WeirWeather/WeirWeather-AWS/minutes/Group Meetings/Group Meeting 9 - 04-10-19.pdf

04/11/19 | Meeting Minutes | WeirWeather
Group Meeting 9 | 1

# WeirWeather Group Meeting 9 Minutes

Date: 11:00, Mon 04/11/19 | Room: RC473
Minute Taker: Tesfu Gebremedhin

## 1 Attendance

Zack North, Callum Brooksby, Tesfu Gebremedhin, Alexander Ulrichsen, Mario Manca

## 2 Announcements

Only having one meeting every week on Mondays

## 3 Review Previous Meeting Minutes

The previous meeting’s minutes were reviewed and accepted by the group.

## 4 Actions from Last Meeting

# | Action | Assigned To | Progress

1 | Competitor Analysis | All | Done
2 | Background Research Tasks | All | Done

## 5 Agenda

- Update meeting
- Check logbooks
- Decide actions for next week

## 6 Actions

# | Action | Assigned To | Progress

1 | Complete PDS | All | Done
2 | Organise Roof Access | Alexander | Done
3 | Create a database | Alexander | Done
4 | Email Professor Macdonald regarding web server | Alexander | Done
5 | Wind Speed Requirements | Tesfu | Done
6 | Wind Direction Requirements | Tesfu | Done
7 | Daylight Hours Requirements | Tesfu | Done
8 | Web Server Requirements | Callum | Done
9 | Website GUI Requirements | Callum | Done
10 | Microcontroller Requirements | Zack | Done

04/11/19 | Meeting Minutes | WeirWeather
Group Meeting 9 | 2
11 | Solar Panel Requirements | Zack | 08/11/19
12 | Battery & Controller Requirements | Zack | 08/11/19
13 | Rain Gauge Requirements | Mario | 08/11/19
14 | Temperature and Humidity Requirements | Mario | 08/11/19
15 | Barometric Pressure Requirements | Mario | 08/11/19
