WeirWeather/WeirWeather-AWS/software/Website/Images/james.png

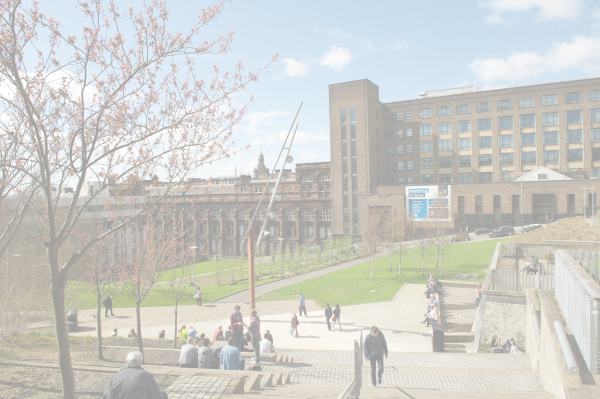
software/Website/Images/james.png
