WeirWeather/WeirWeather-AWS/hardware/Complete CAD Assembly/3D Print/Wind Vane Print.stl

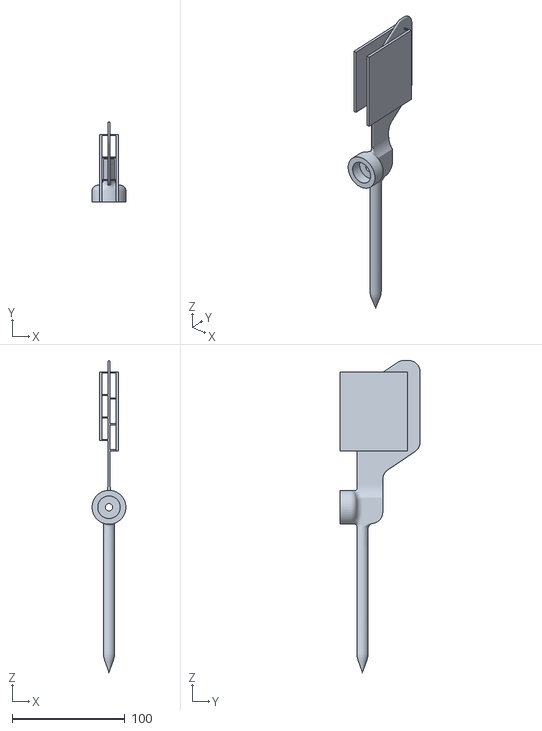
[picture p27: CAD file, 2020-04-21]
hardware/Complete CAD Assembly/3D Print/Wind Vane Print.stl
30.0 x 71.0 x 276.4
