WeirWeather/WeirWeather-AWS/hardware/Complete CAD Assembly/PCB CAD/anemometer_v4.step

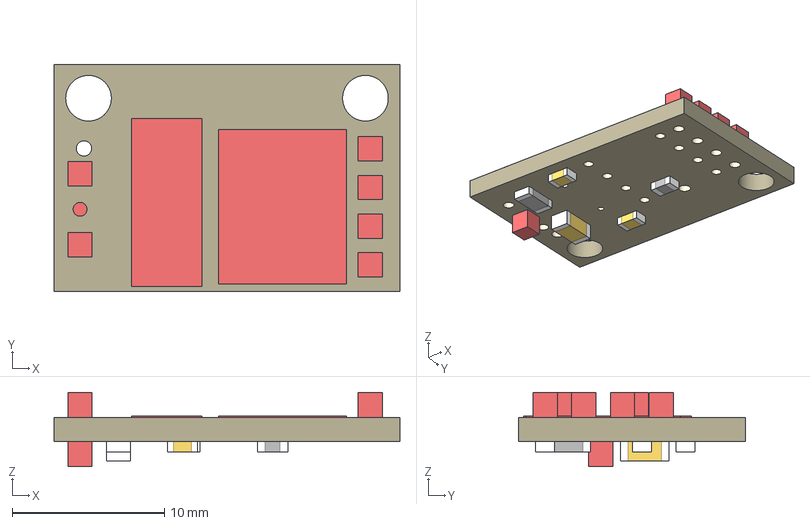
[picture p28: CAD file, 2020-04-21]
hardware/Complete CAD Assembly/PCB CAD/anemometer_v4.step
22.7 x 14.9 x 4.89 mm
Board
1,6/0,9 x 7
4.7k
100n
ATTINY85-P
QCL16.0000F18B23B
18 pF x 2
10k
