WeirWeather/WeirWeather-AWS/hardware/Complete CAD Assembly/Radiation Sheild/HTU21D_mount_V1.stl

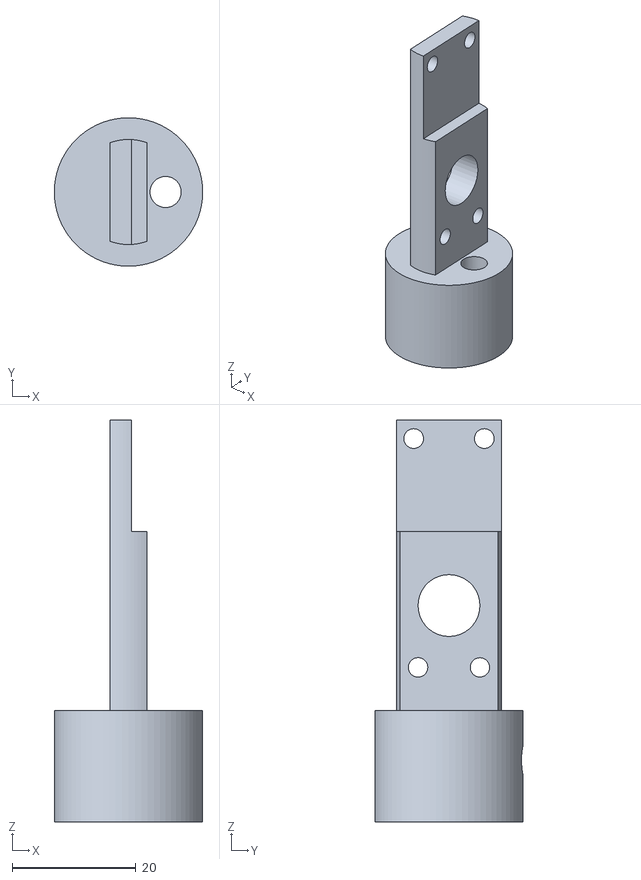
[picture p29: CAD file, 2020-04-21]
hardware/Complete CAD Assembly/Radiation Sheild/HTU21D_mount_V1.stl
24.0 x 24.0 x 65.0
