WeirWeather/WeirWeather-AWS/hardware/Rain Gauge/CAD/STLs/Base.stl

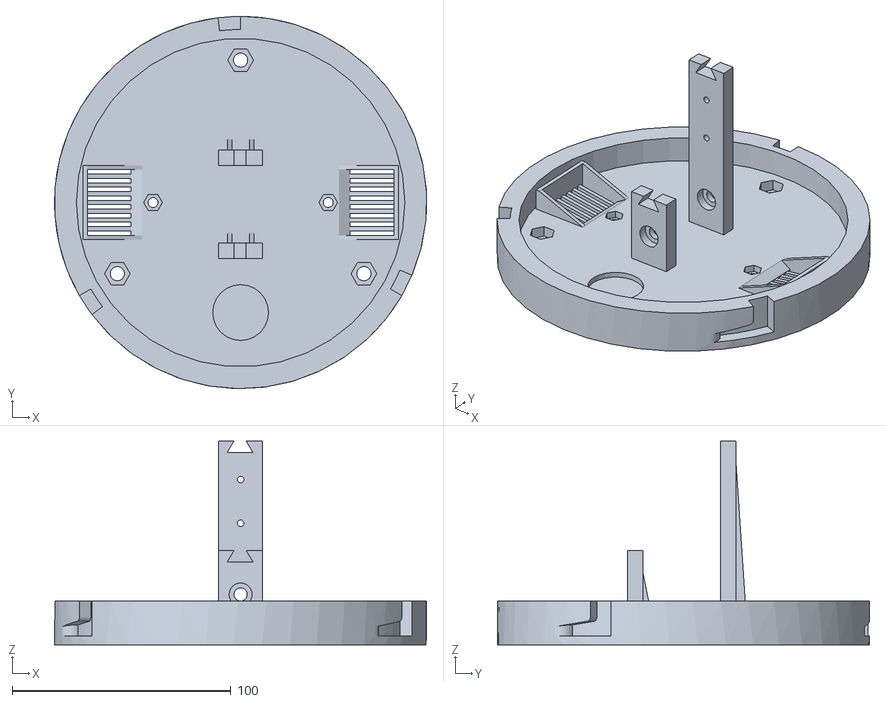
[picture p30: CAD file, 2020-04-16]
hardware/Rain Gauge/CAD/STLs/Base.stl
169.9 x 170.0 x 93.0
