WeirWeather/WeirWeather-AWS/hardware/Complete CAD Assembly/3D Print/Bottom.stl

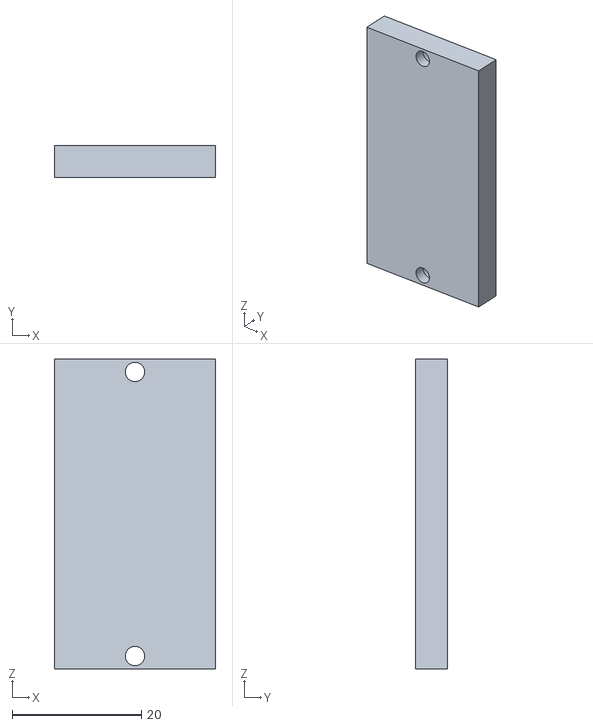
[picture p31: CAD file, 2020-04-21]
hardware/Complete CAD Assembly/3D Print/Bottom.stl
25.0 x 5.00 x 48.0
