WeirWeather/WeirWeather-AWS/hardware/Complete CAD Assembly/PCB CAD/Four_Sensors_V2.step

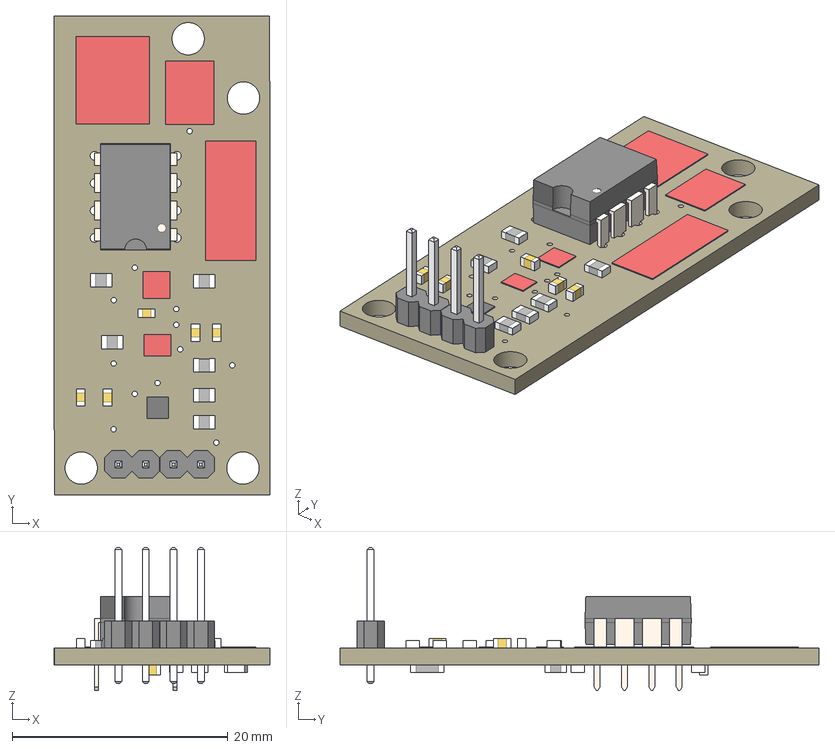
[picture p32: CAD file, 2020-04-21]
hardware/Complete CAD Assembly/PCB CAD/Four_Sensors_V2.step
20.0 x 44.4 x 13.3 mm
Board
DIL08
100 nF x 6
18 pF x 2
1X02 x 2
1K x 2
10K x 7
SHT35
TMP117
DSP310XTSA1
QCL16.0000F18B23B
3306F-1-103
JST-PH2
