WeirWeather/WeirWeather-AWS/hardware/Rain Gauge/CAD/STLs/PCB_Holder_Lid.stl

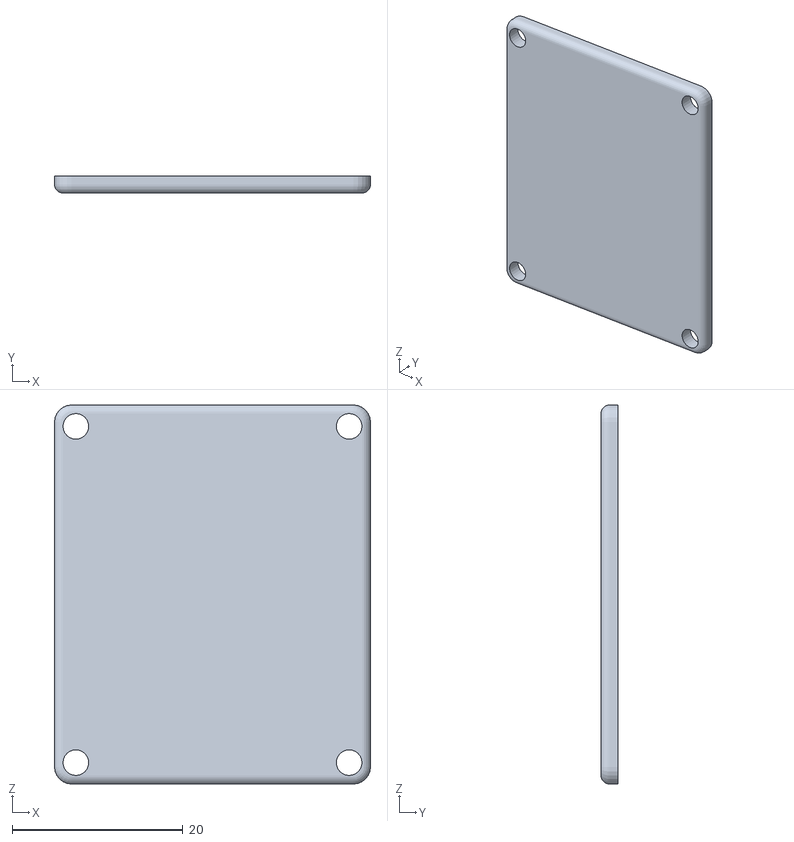
[picture p33: CAD file, 2020-04-16]
hardware/Rain Gauge/CAD/STLs/PCB_Holder_Lid.stl
37.0 x 2.00 x 44.4
