WeirWeather/WeirWeather-AWS/hardware/Complete CAD Assembly/3D Print/Disk-3.stl

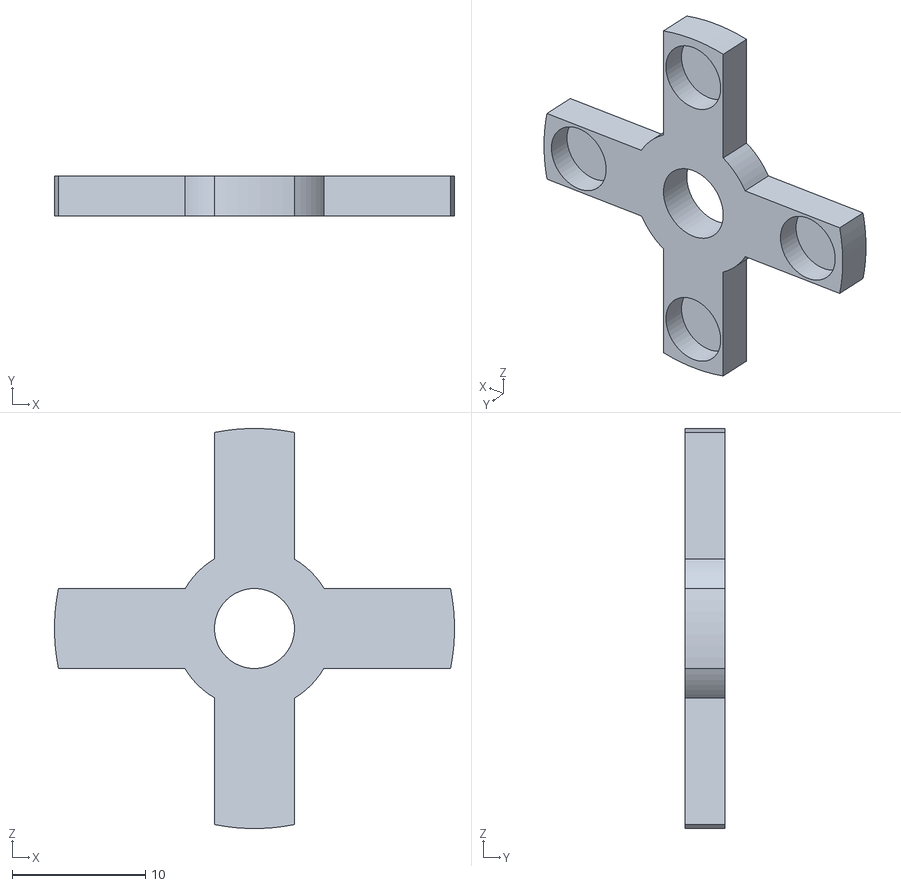
[picture p34: CAD file, 2020-04-21]
hardware/Complete CAD Assembly/3D Print/Disk-3.stl
30.0 x 3.00 x 30.0
