WeirWeather/WeirWeather-AWS/hardware/Complete CAD Assembly/Radiation Sheild/Rad_Shd_Horz_mount_V1.stl

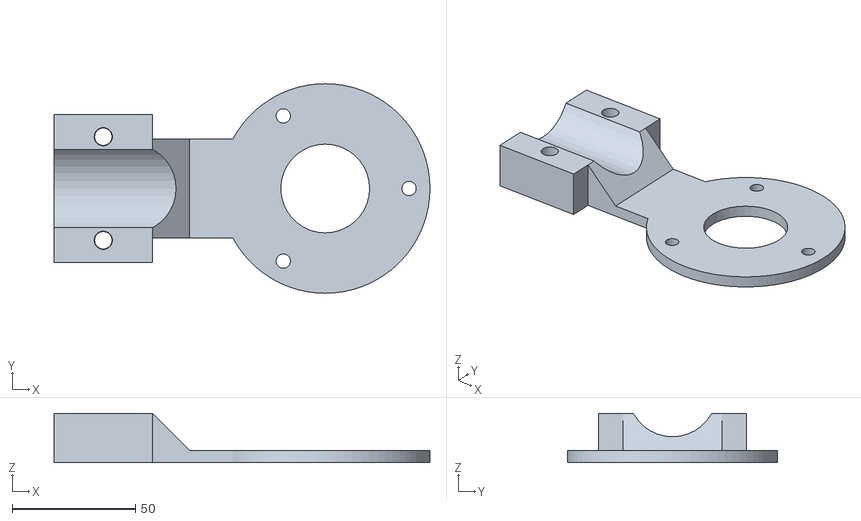
[picture p35: CAD file, 2020-04-21]
hardware/Complete CAD Assembly/Radiation Sheild/Rad_Shd_Horz_mount_V1.stl
152.5 x 85.0 x 20.0
