WeirWeather/WeirWeather-AWS/hardware/Rain Gauge/CAD/STLs/Collector_2_of_4.stl

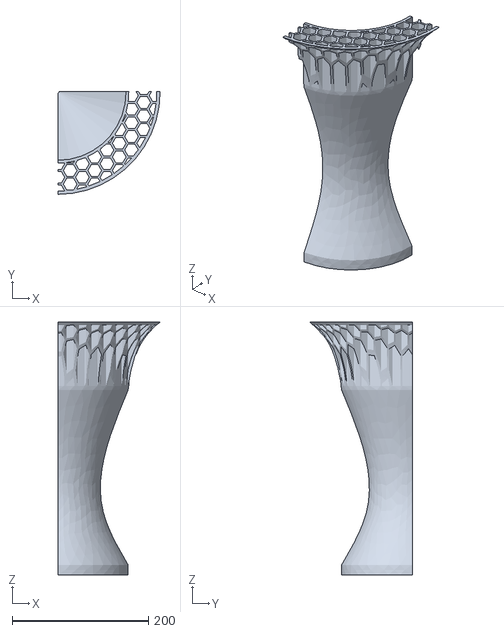
[picture p36: CAD file, 2020-04-16]
hardware/Rain Gauge/CAD/STLs/Collector_2_of_4.stl
150.0 x 150.7 x 371.2
