WeirWeather/WeirWeather-AWS/hardware/Complete CAD Assembly/3D Print/Wind Vane.stl

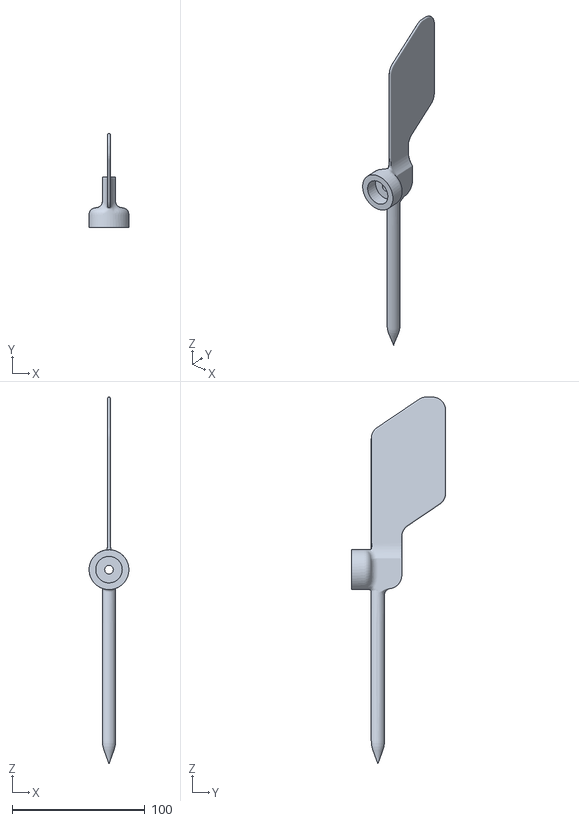
[picture p37: CAD file, 2020-04-21]
hardware/Complete CAD Assembly/3D Print/Wind Vane.stl
30.0 x 71.0 x 276.4
