WeirWeather/WeirWeather-AWS/hardware/Complete CAD Assembly/Radiation Sheild/SHT15_mount_V1.stl

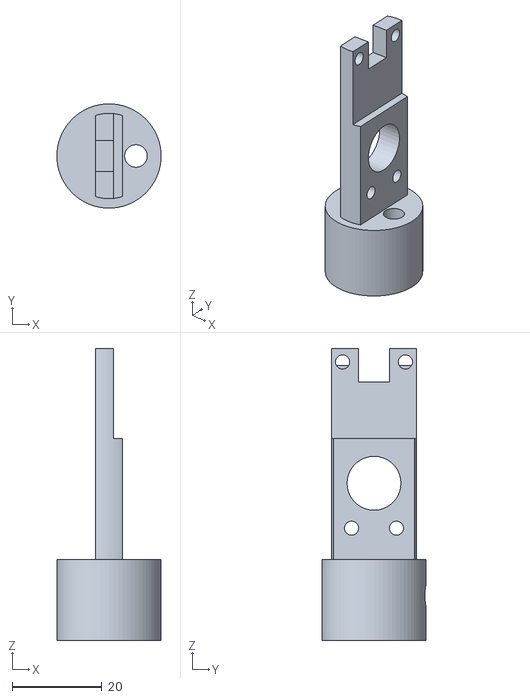
[picture p38: CAD file, 2020-04-21]
hardware/Complete CAD Assembly/Radiation Sheild/SHT15_mount_V1.stl
23.2 x 23.2 x 65.0
