WeirWeather/WeirWeather-AWS/hardware/Rain Gauge/CAD/STLs/Funel_2_of_2.stl

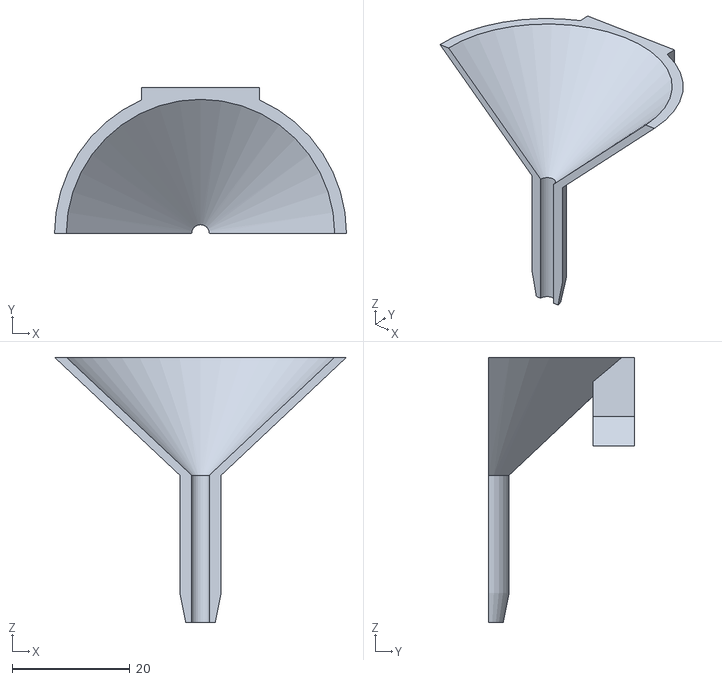
[picture p39: CAD file, 2020-04-16]
hardware/Rain Gauge/CAD/STLs/Funel_2_of_2.stl
49.5 x 24.8 x 45.0
