WeirWeather/WeirWeather-AWS/hardware/Rain Gauge/CAD/STLs/Funel_1_of_2.stl

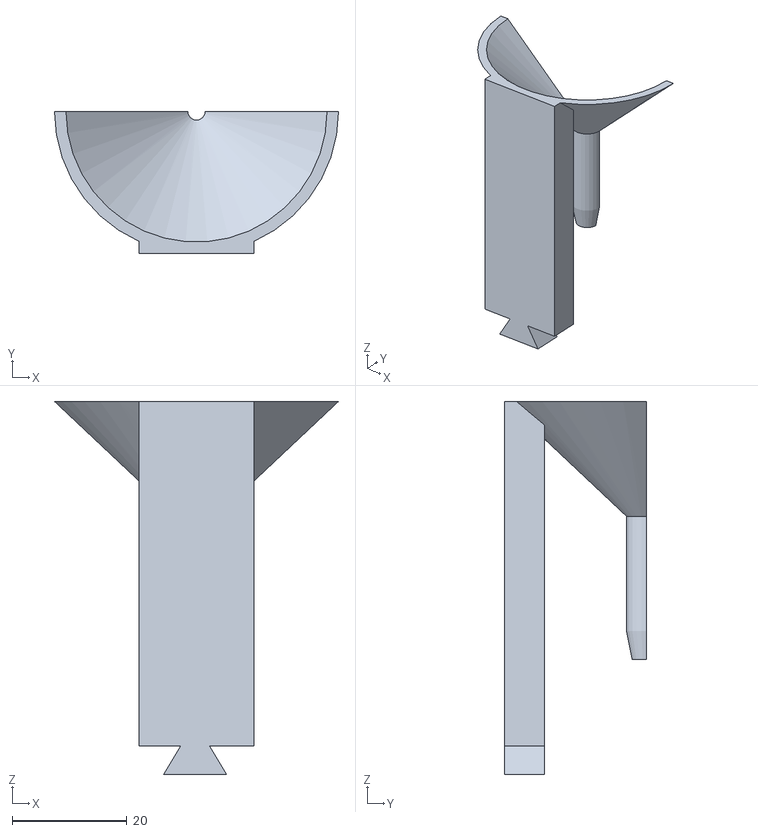
[picture p41: CAD file, 2020-04-16]
hardware/Rain Gauge/CAD/STLs/Funel_1_of_2.stl
49.5 x 24.8 x 65.0
