WeirWeather/WeirWeather-AWS/hardware/Complete CAD Assembly/3D Print/Cap.stl

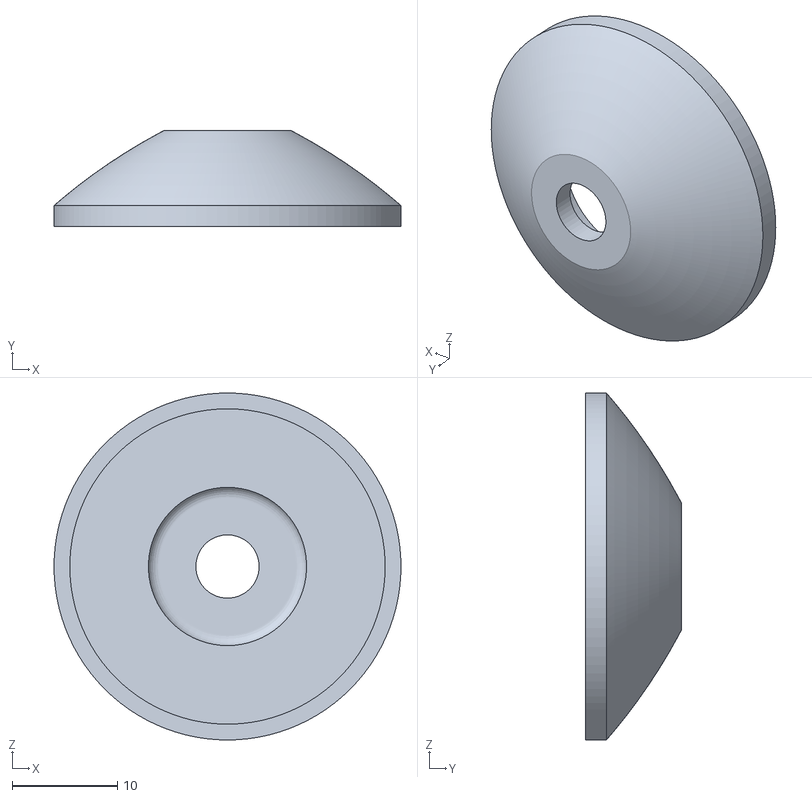
[picture p42: CAD file, 2020-04-21]
hardware/Complete CAD Assembly/3D Print/Cap.stl
32.9 x 9.12 x 32.9
