WeirWeather/WeirWeather-AWS/hardware/Complete CAD Assembly/Radiation Sheild/Rad_Shd_Base_V1.stl

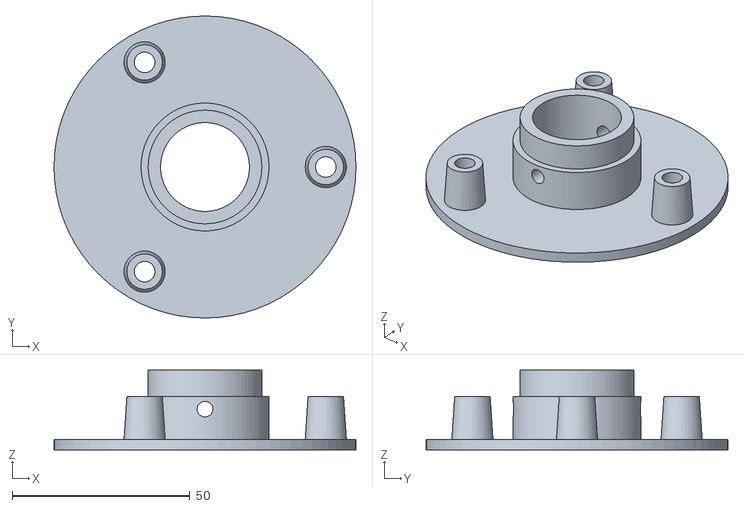
[picture p43: CAD file, 2020-04-16]
hardware/Complete CAD Assembly/Radiation Sheild/Rad_Shd_Base_V1.stl
85.0 x 85.0 x 22.5
