WeirWeather/WeirWeather-AWS/hardware/Complete CAD Assembly/3D Print/Scoops.stl

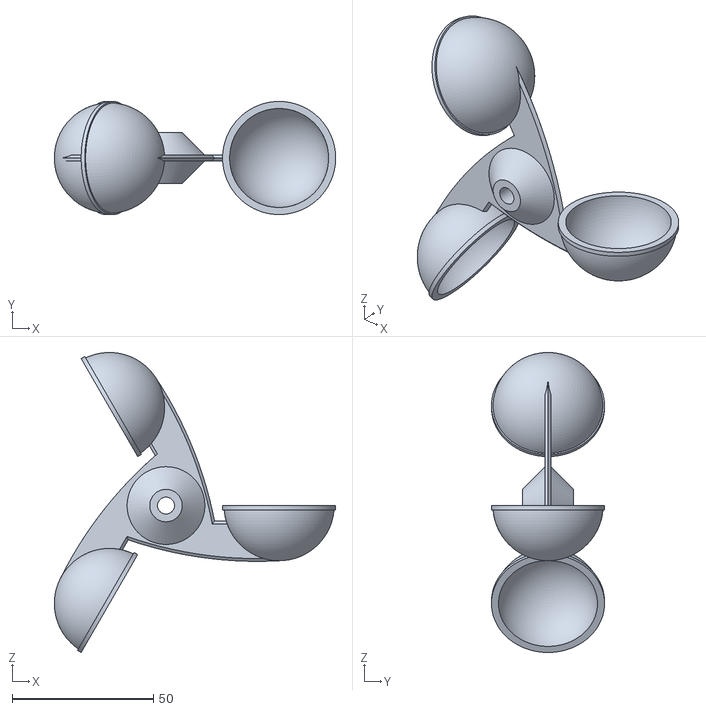
[picture p44: CAD file, 2020-04-21]
hardware/Complete CAD Assembly/3D Print/Scoops.stl
99.5 x 40.0 x 106.1
