WeirWeather/WeirWeather-AWS/hardware/Complete CAD Assembly/Radiation Sheild/Rad_Shd_Top_V1.stl

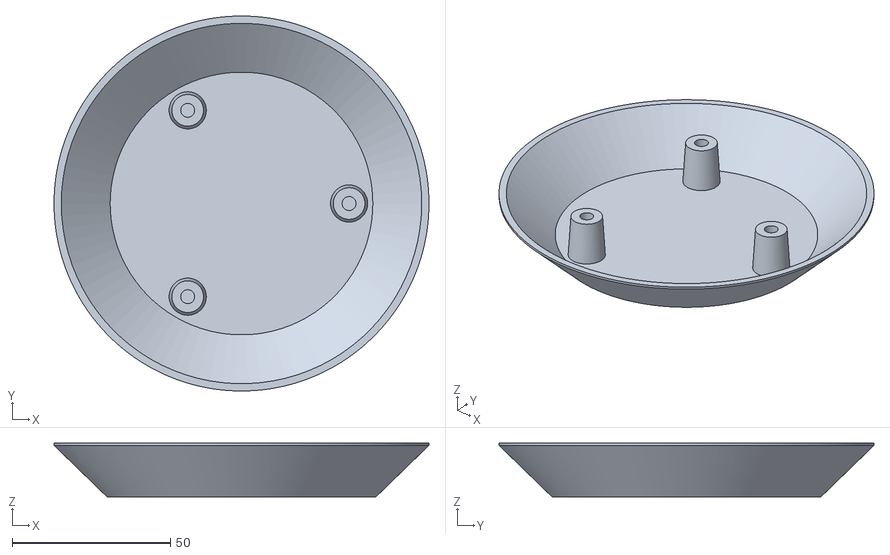
[picture p45: CAD file, 2020-04-16]
hardware/Complete CAD Assembly/Radiation Sheild/Rad_Shd_Top_V1.stl
118.5 x 118.5 x 17.0
