WeirWeather/WeirWeather-AWS/hardware/Complete CAD Assembly/3D Print/Bottom-1.stl

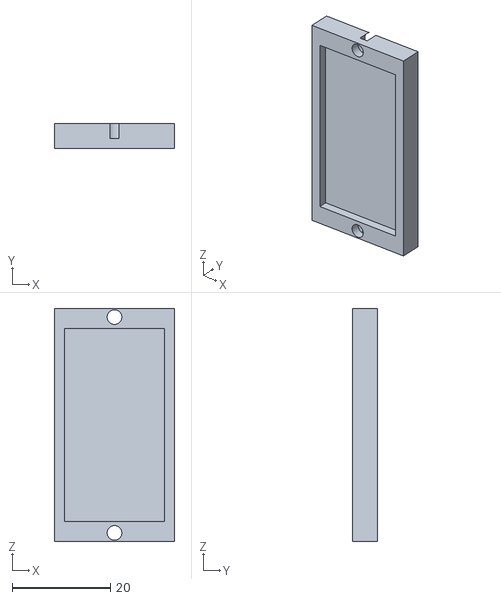
[picture p46: CAD file, 2020-04-21]
hardware/Complete CAD Assembly/3D Print/Bottom-1.stl
24.5 x 5.00 x 47.5
