WeirWeather/WeirWeather-AWS/hardware/Complete CAD Assembly/3D Print/Disk-4.stl

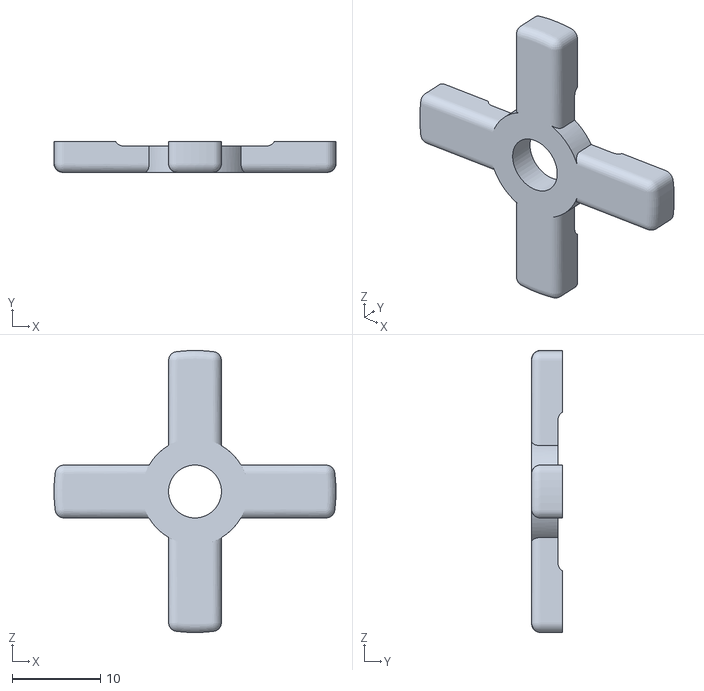
[picture p47: CAD file, 2020-04-21]
hardware/Complete CAD Assembly/3D Print/Disk-4.stl
32.0 x 3.50 x 32.0
