WeirWeather/WeirWeather-AWS/hardware/Complete CAD Assembly/3D Print/Base.stl

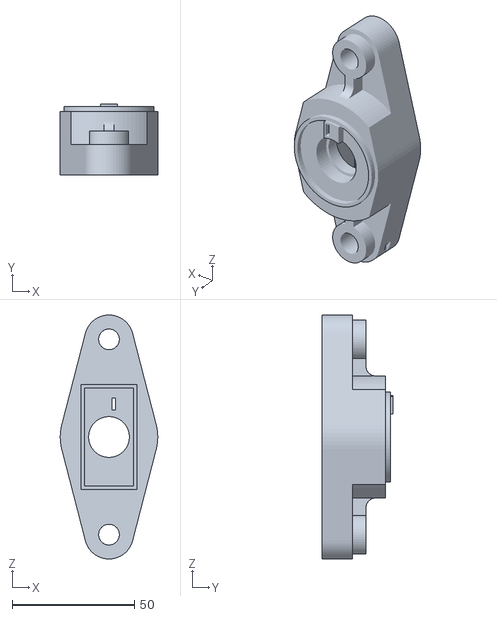
[picture p48: CAD file, 2020-04-21]
hardware/Complete CAD Assembly/3D Print/Base.stl
40.0 x 29.0 x 100.0
