WeirWeather/WeirWeather-AWS/hardware/Complete CAD Assembly/Main Enclosure/panel-connector/Renderings/DBConnector.jpg

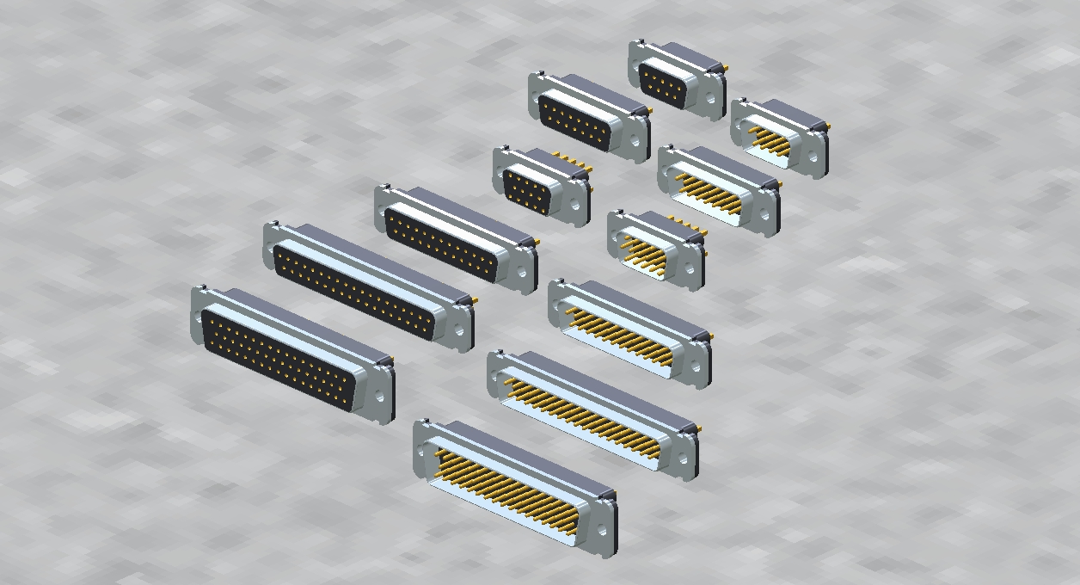
hardware/Complete CAD Assembly/Main Enclosure/panel-connector/Renderings/DBConnector.jpg
