WeirWeather/WeirWeather-AWS/hardware/Complete CAD Assembly/Solar Panel/blue-electric-solar-panel-seamless-pattern-vector.jpg

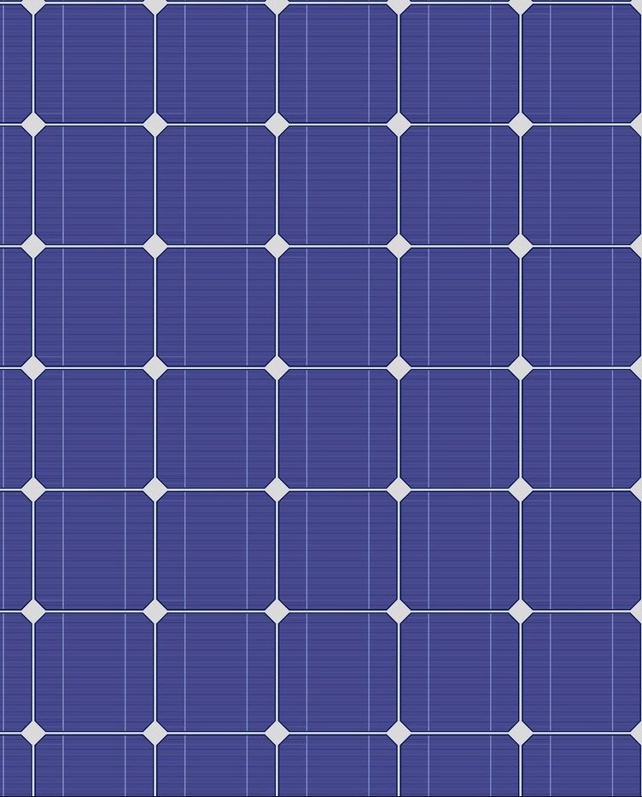
hardware/Complete CAD Assembly/Solar Panel/blue-electric-solar-panel-seamless-pattern-vector.jpg
