WeirWeather/WeirWeather-AWS/hardware/Complete CAD Assembly/Solar Panel/Picture1.png

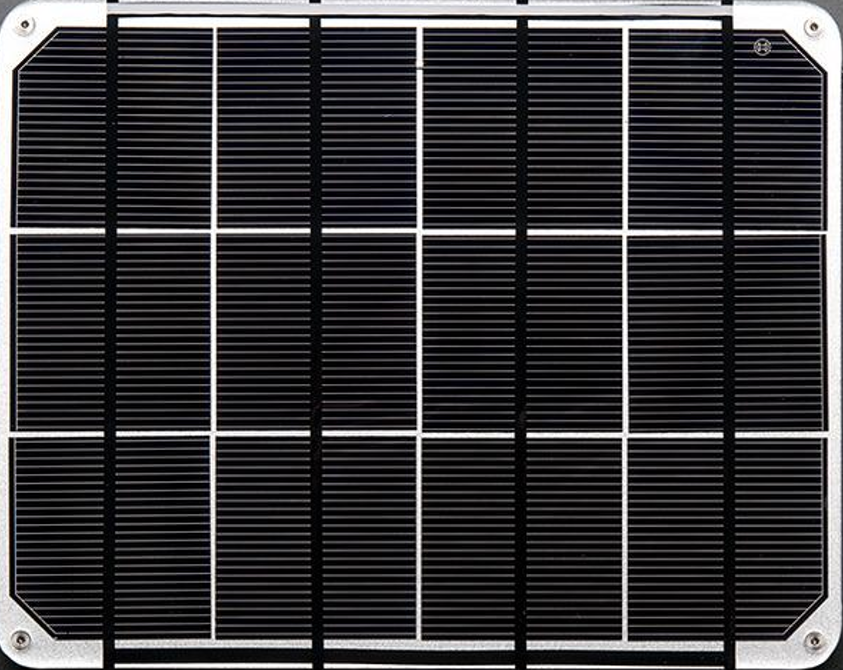
hardware/Complete CAD Assembly/Solar Panel/Picture1.png
