WeirWeather/WeirWeather-AWS/hardware/Complete CAD Assembly/Solar Panel/Nutsert Drawing.pdf

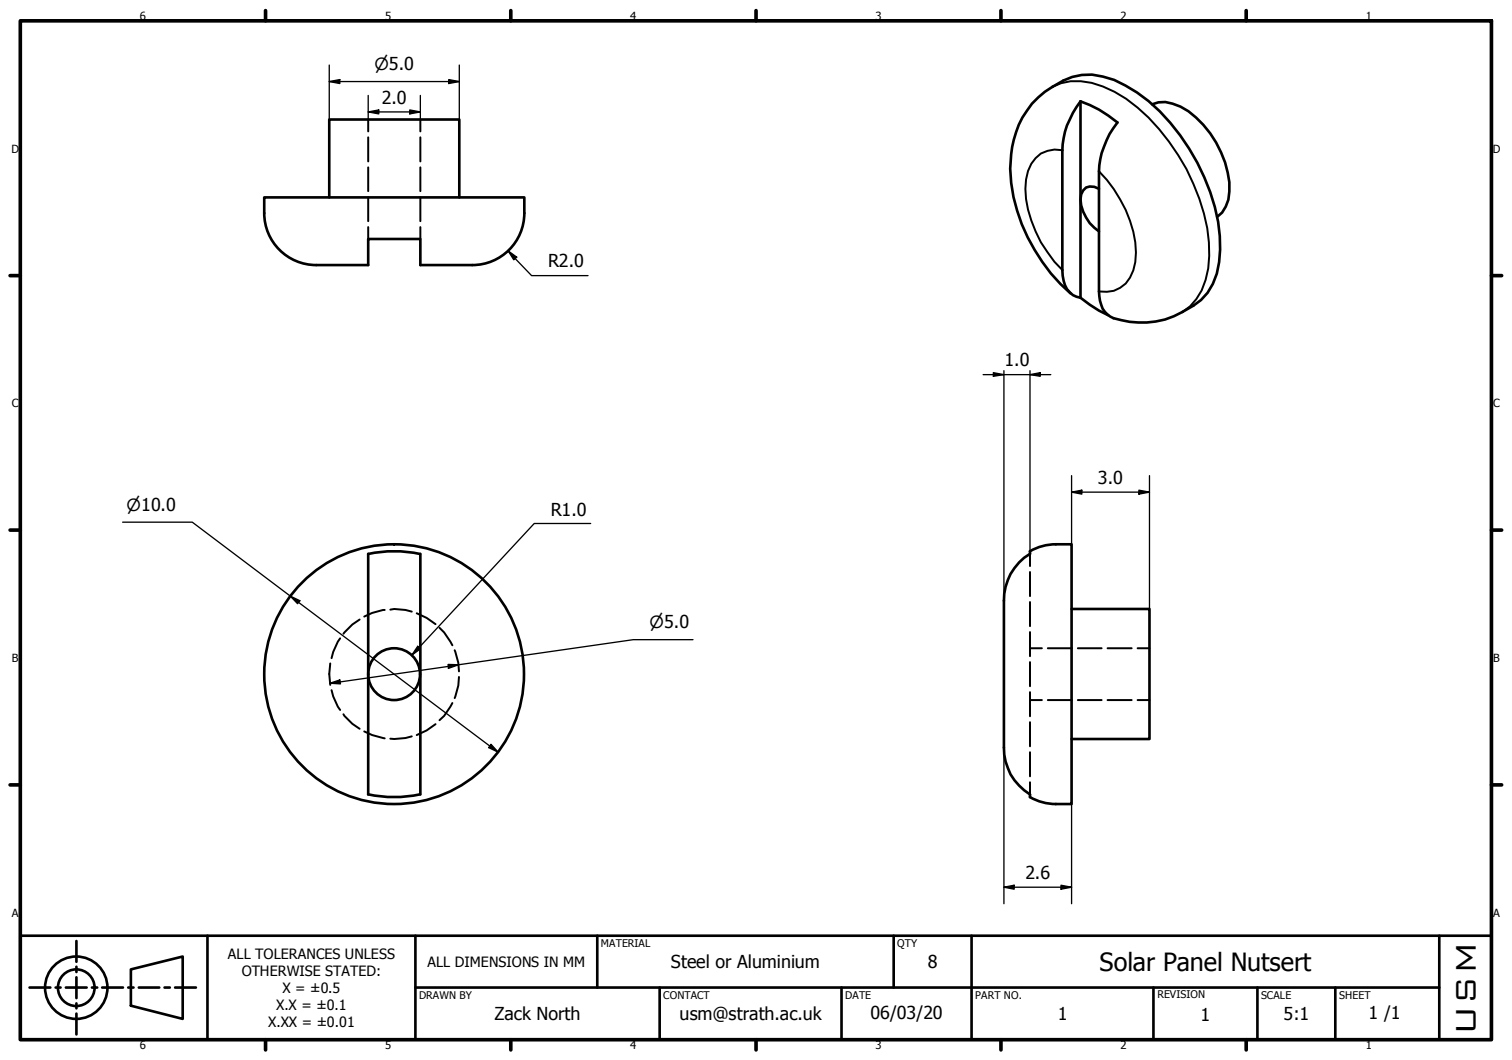
[picture p56: page 1]

ALL TOLERANCES UNLESS OTHERWISE STATED: X = ±0.5 X.X = ±0.1 X.XX = ±0.01 | ALL DIMENSIONS IN MM | MATERIAL Steel or Aluminium | QTY 8 | Solar Panel Nutsert | M

DRAWN BY Zack North | CONTACT usm@strath.ac.uk | DATE 06/03/20 | PART NO. 1 | REVISION 1 | SCALE 5:1 | SHEET 1 /1
