WeirWeather/WeirWeather-AWS/hardware/Complete CAD Assembly/Drawings/Base.pdf

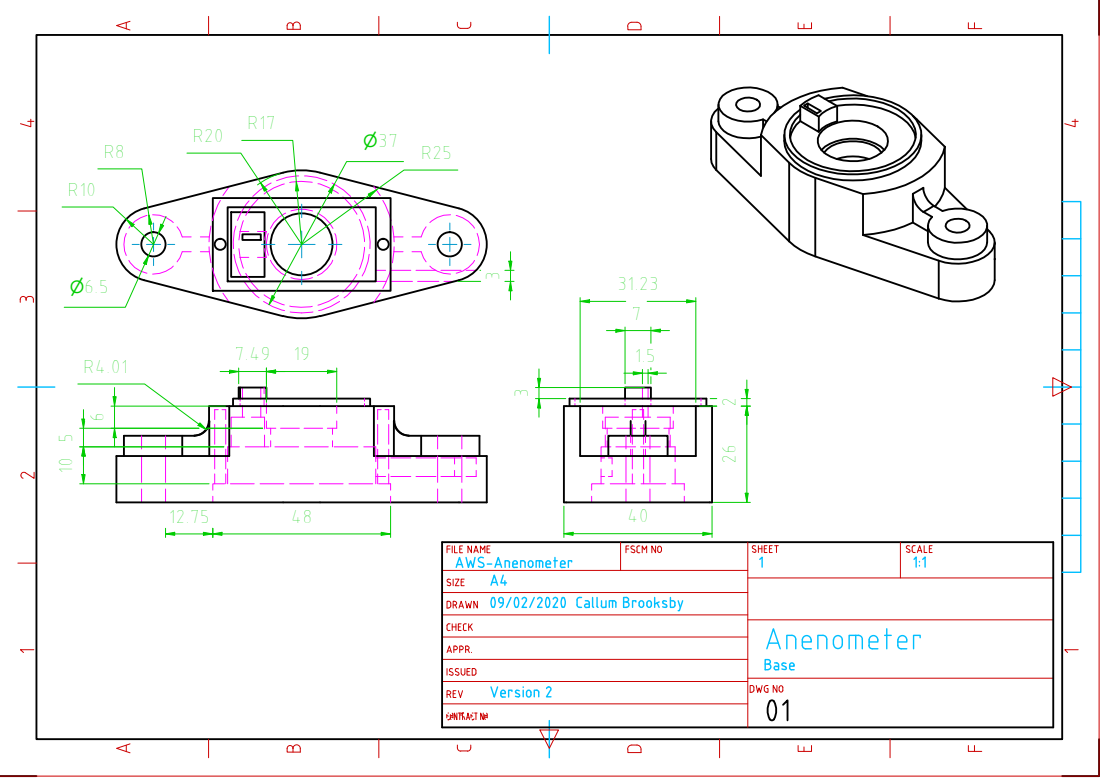
[picture p57: page 1]
