WeirWeather/WeirWeather-AWS/hardware/Complete CAD Assembly/Drawings/Body.pdf

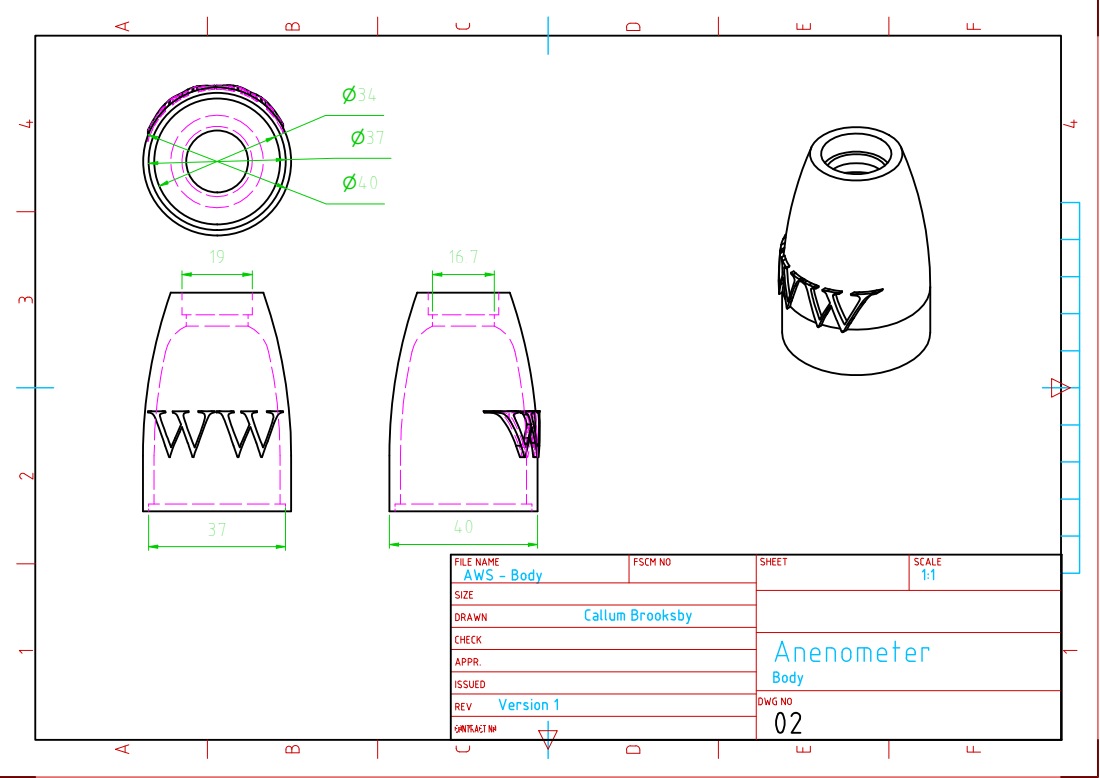
[picture p58: page 1]
