WeirWeather/WeirWeather-AWS/hardware/Complete CAD Assembly/Drawings/Bottom Mount.pdf

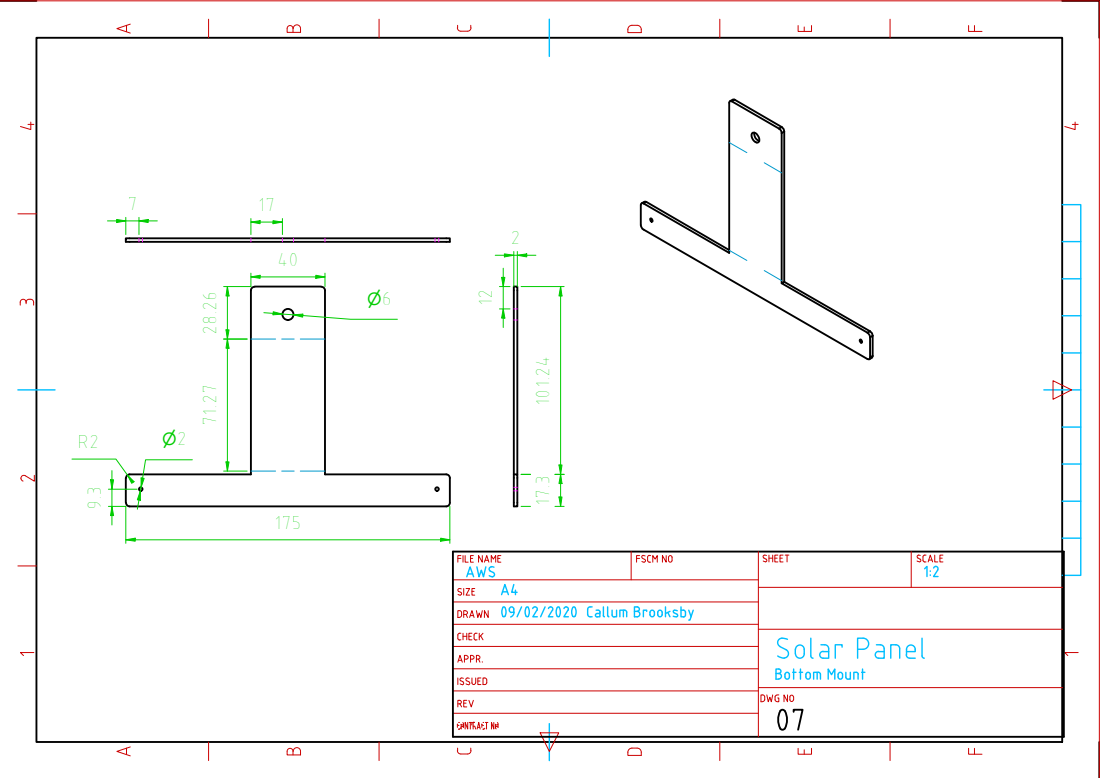
[picture p59: page 1]
