WeirWeather/WeirWeather-AWS/hardware/Complete CAD Assembly/Drawings/Cap.pdf

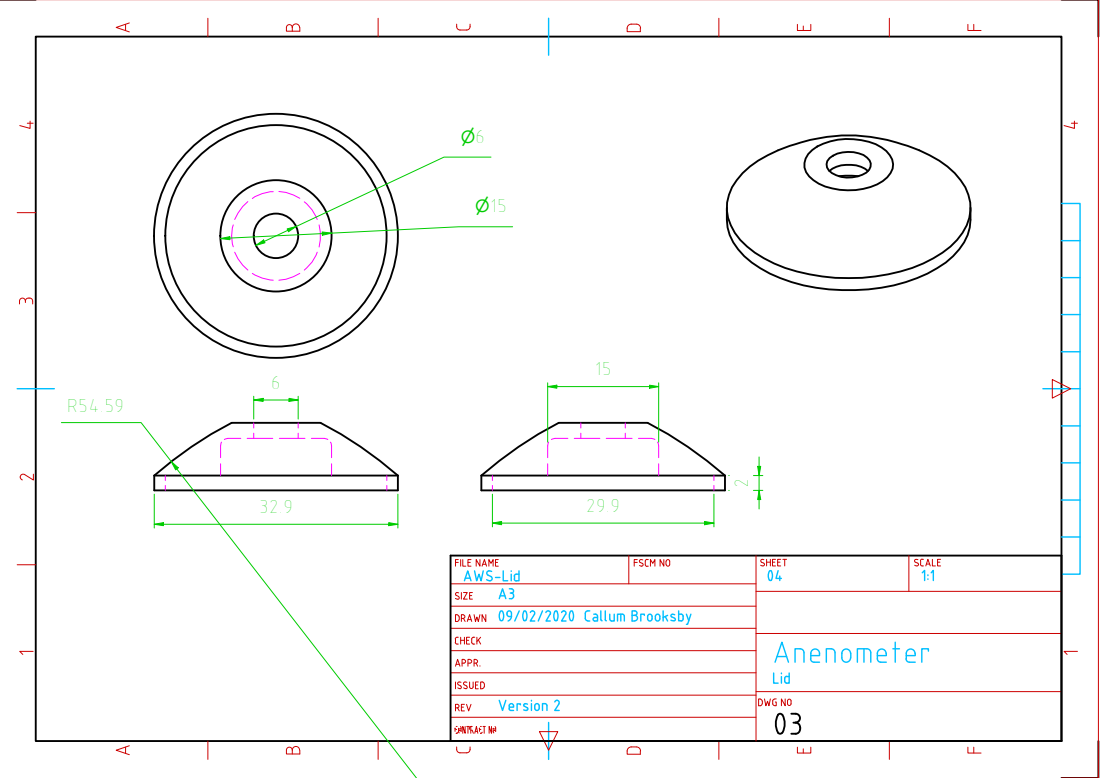
[picture p60: page 1]
