WeirWeather/WeirWeather-AWS/hardware/Complete CAD Assembly/Drawings/Main Enclosure Base.pdf

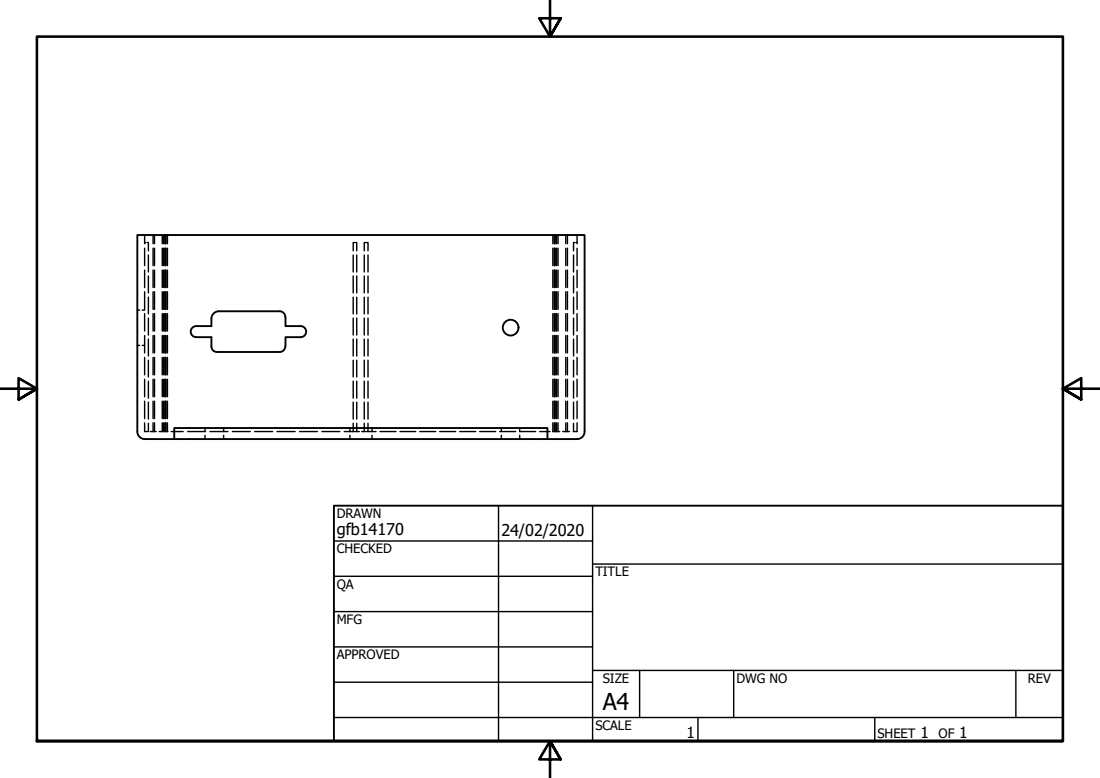
[picture p61: page 1]
