WeirWeather/WeirWeather-AWS/hardware/Complete CAD Assembly/Drawings/Scoops.pdf

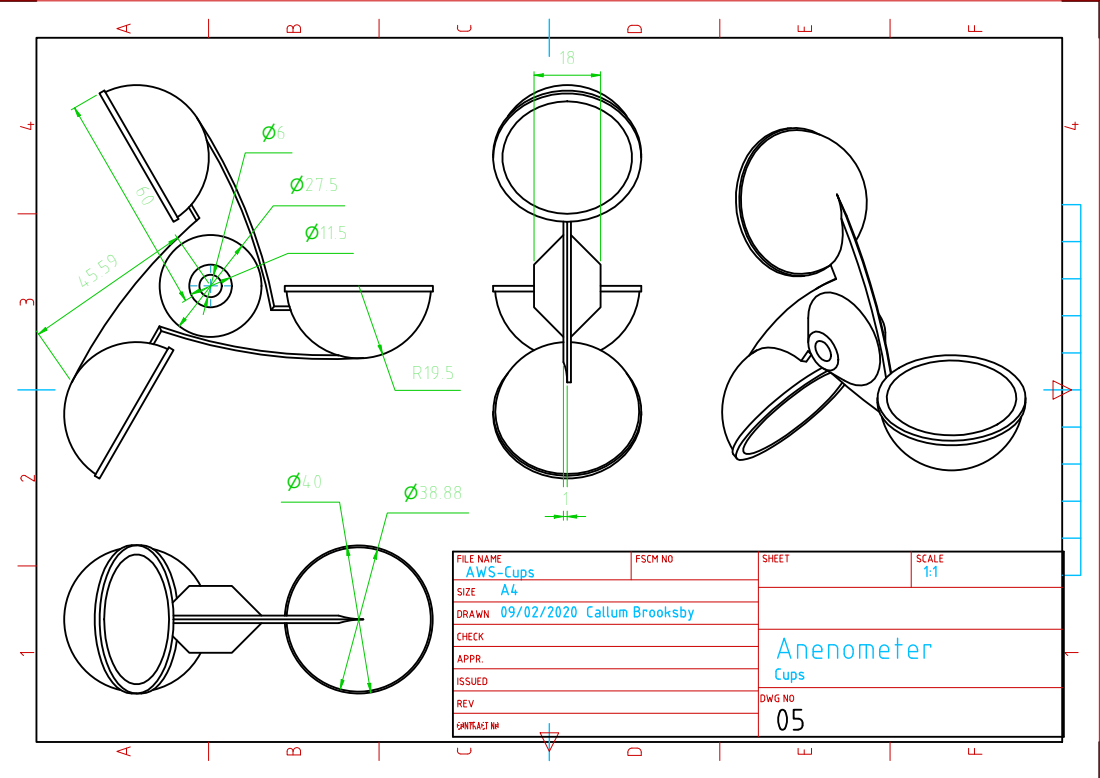
[picture p62: page 1]
