WeirWeather/WeirWeather-AWS/hardware/Complete CAD Assembly/Drawings/SolarPanelTopMount.pdf

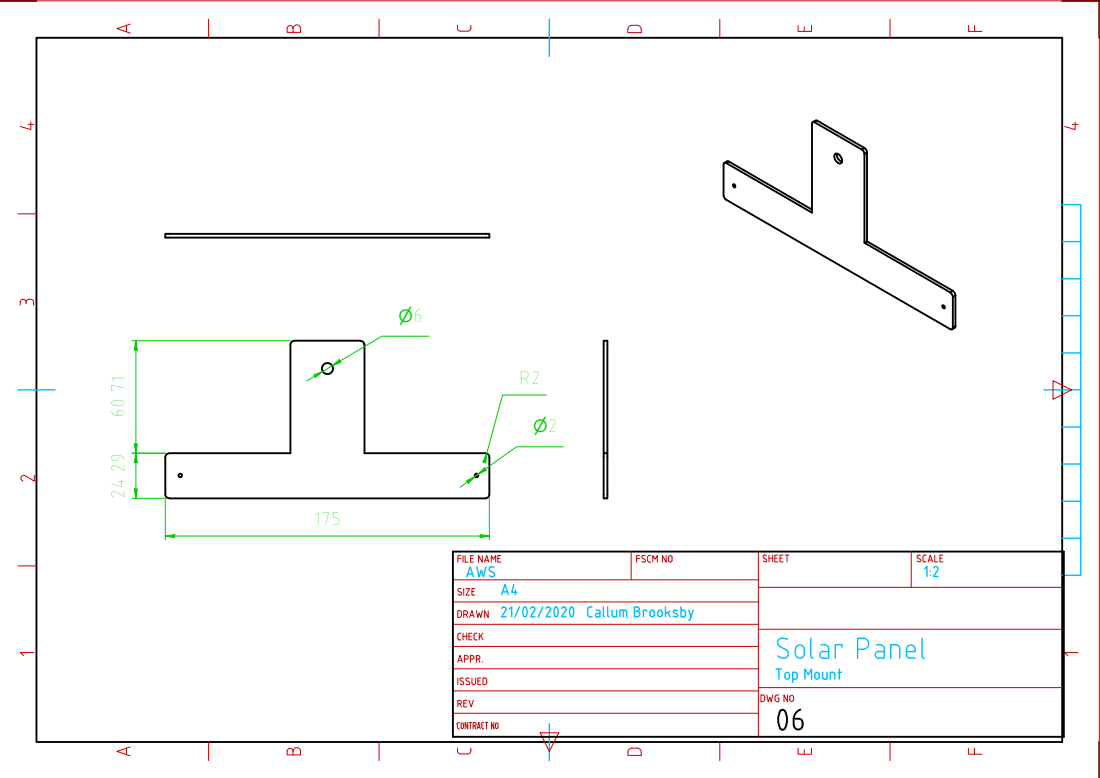
[picture p63: page 1]
