WeirWeather/WeirWeather-AWS/hardware/Complete CAD Assembly/Drawings/Top Mount.pdf

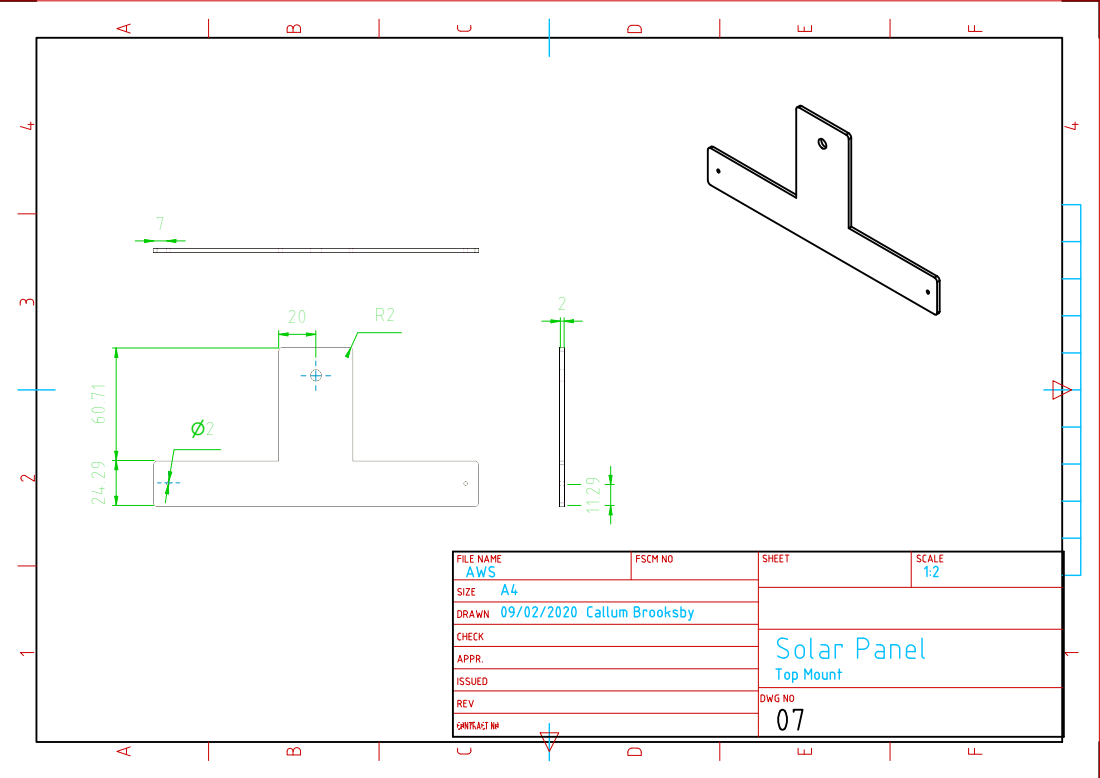
[picture p64: page 1]
